Brabudu/ElectroneddasV3/Electronic_Electroneddas/ElectroV3_2_1.kicad_sch

## KiCad design Electronic_Electroneddas/ElectroV3_2_1.kicad_sch (2024-02-18)

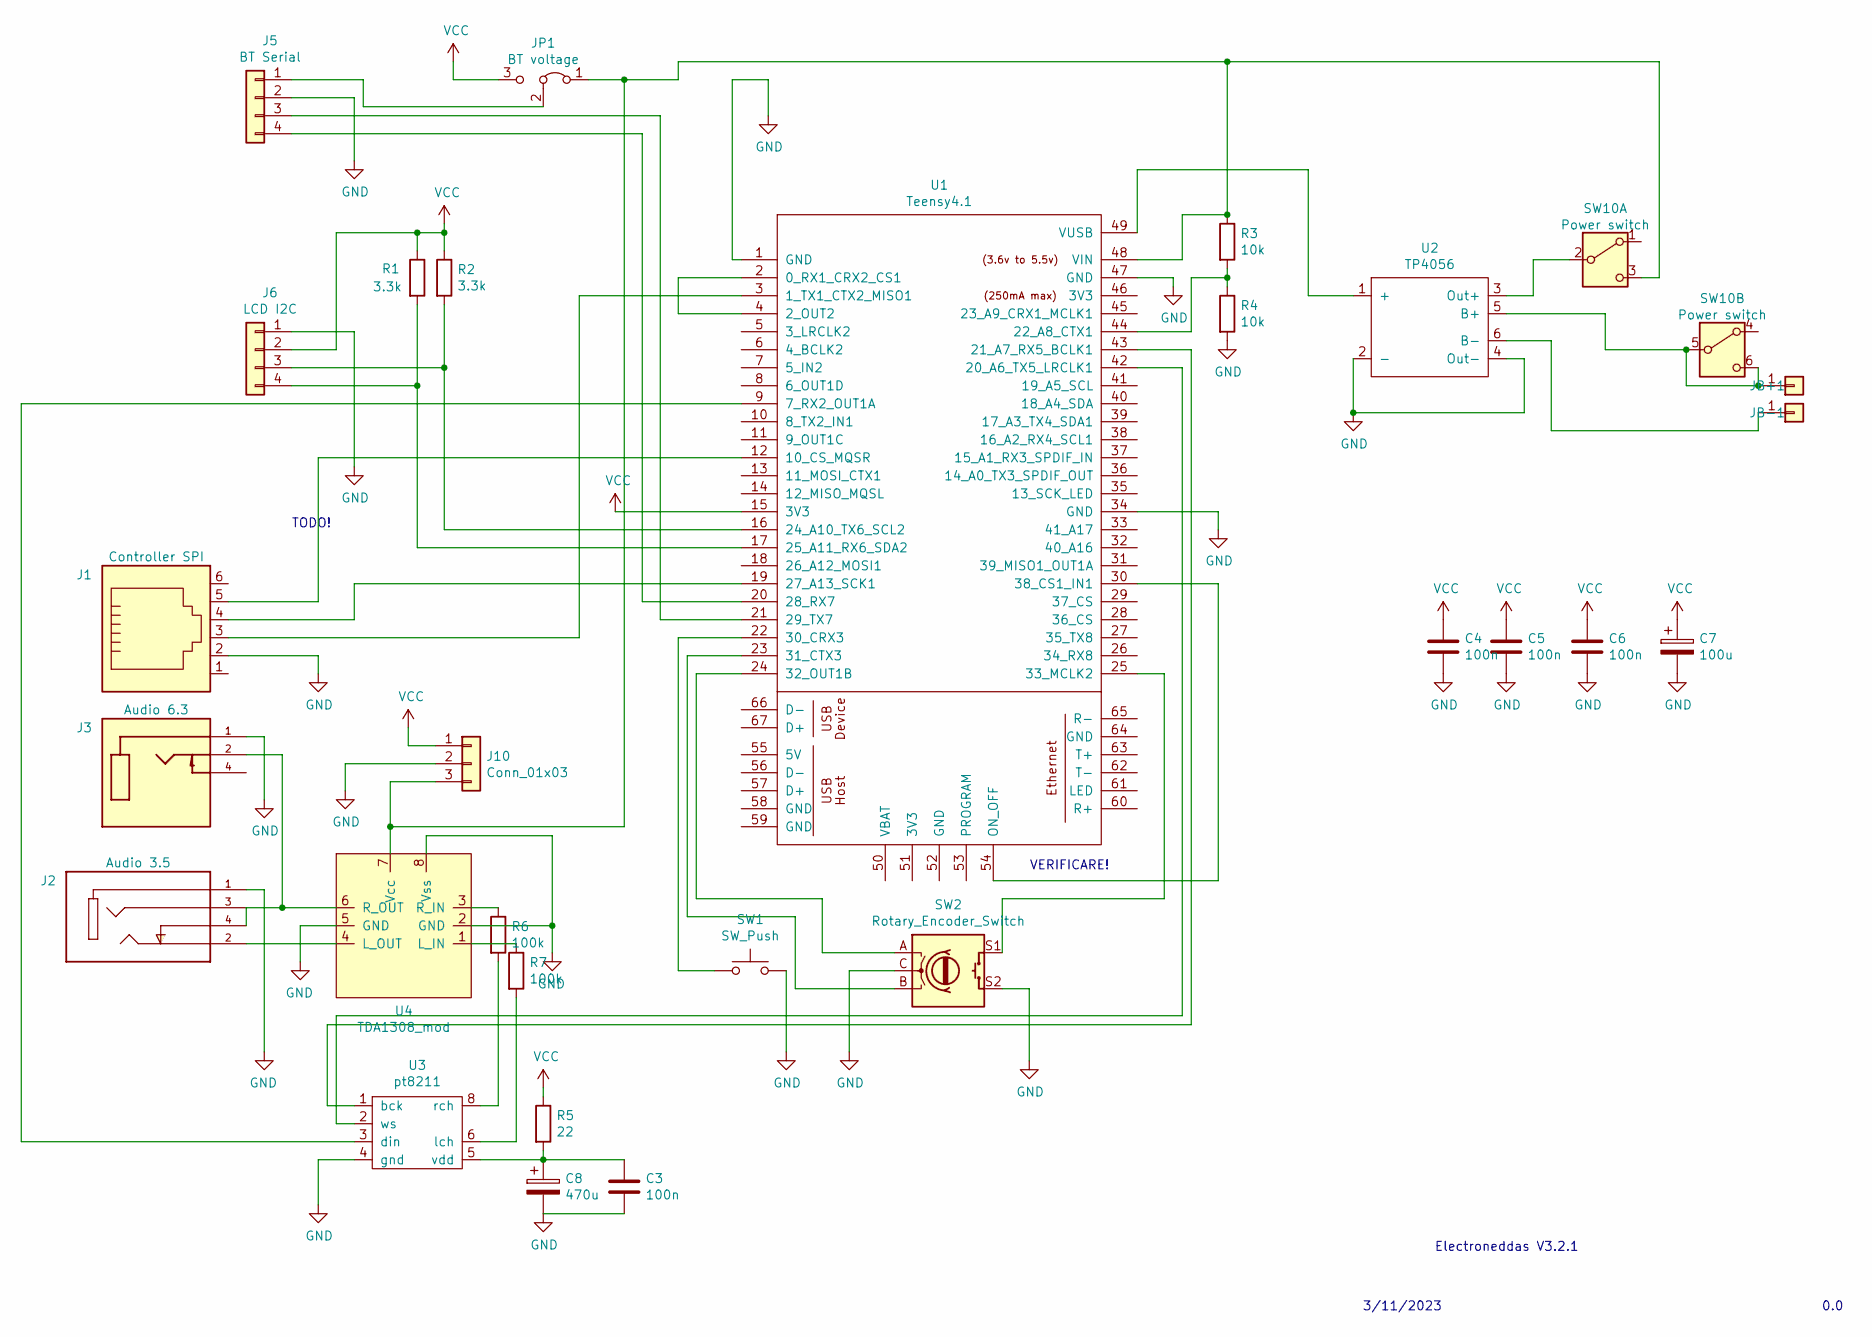
[picture p26: schematic ElectroV3_2_1.kicad_sch]

Parts:
C3, C4, C5, C6: 100n; C_Disc_D6.0mm_W2.5mm_P5.00mm
C7: 100u; CP_Radial_D8.0mm_P3.50mm
C8: 470u; CP_Radial_D8.0mm_P3.50mm
J1: Controller SPI; RJ12_Amphenol_54601
J2: Audio 3.5; CUI_SJ1-3534NG
J3: Audio 6.3; CUI_MJ-63022B; PARTREV 1.0
J5: BT Serial; PinHeader_1x04_P2.54mm_Vertical
J6: LCD I2C; PinHeader_1x04_P2.54mm_Vertical
J10: Conn_01x03; PinHeader_1x03_P2.54mm_Vertical
JB+1: Conn_01x01_Male; PinHeader_1x01_P2.54mm_Vertical
JB-1: Conn_01x01_Male; PinHeader_1x01_P2.54mm_Vertical
JP1: BT voltage; SolderJumper-3_P1.3mm_Bridged12_Pad1.0x1.5mm
R1, R2: 3.3k; R_Axial_DIN0207_L6.3mm_D2.5mm_P2.54mm_Vertical
R3, R4: 10k; R_Axial_DIN0207_L6.3mm_D2.5mm_P2.54mm_Vertical
R5: 22; R_Axial_DIN0207_L6.3mm_D2.5mm_P2.54mm_Vertical
R6, R7: 100k; R_Axial_DIN0207_L6.3mm_D2.5mm_P2.54mm_Vertical
SW1: SW_Push; SW_PUSH_6mm
SW2: Rotary_Encoder_Switch; RotaryEncoder_Alps_EC11E-Switch_Vertical_H20mm_CircularMoun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
SW10: Power switch; 6pin_vertical
U1: Teensy4.1; Teensy41
U2: TP4056
U3: pt8211; SOIC-8_3.9x4.9mm_P1.27mm
U4: TDA1308_mod; TDA1308

Connections:
GND: C3.2, C4.2, C5.2, C6.2, C7.2, C8.2, J1.2, J2.1, J3.1, J5.2, J6.1, J10.2, R4.2, SW1.2, SW2.C, SW2.S2, U1.1 (GND), U1.34 (GND), U1.47 (GND), U2.2 (-), U2.4 (Out-), U3.4 (gnd), U4.2 (GND), U4.5 (GND), U4.8 (Vss)
unnamed: C3.1, C8.1, R5.2, U3.5 (vdd)
unnamed: J1.3, U1.3 (1_TX1_CTX2_MISO1)
unnamed: J1.4, U1.19 (27_A13_SCK1)
unnamed: J1.5, U1.12 (10_CS_MQSR)
unnamed: J2.2, U4.4 (L_OUT)
unnamed: J2.3, J2.4, J3.2, U4.6 (R_OUT)
unnamed: J5.1, JP1.2 (C)
unnamed: J5.3, U1.21 (29_TX7)
unnamed: J5.4, U1.20 (28_RX7)
unnamed: J6.3, R2.2, U1.16 (24_A10_TX6_SCL2)
unnamed: J6.4, R1.2, U1.17 (25_A11_RX6_SDA2)
unnamed: J10.3, JP1.1 (A), R3.1, SW10.3 (C), U1.48 (VIN), U4.7 (Vcc)
unnamed: JB+1.1, SW10.5 (B), SW10.6 (C), U2.5 (B+)
unnamed: JB-1.1, U2.6 (B-)
unnamed: R3.2, R4.1, U1.44 (22_A8_CTX1)
unnamed: R6.1, U4.3 (R_IN)
unnamed: R6.2, U3.8 (rch)
unnamed: R7.1, U4.1 (L_IN)
unnamed: R7.2, U3.6 (lch)
unnamed: SW1.1, U1.22 (30_CRX3)
unnamed: SW2.A, U1.24 (32_OUT1B)
unnamed: SW2.B, U1.23 (31_CTX3)
unnamed: SW2.S1, U1.25 (33_MCLK2)
unnamed: SW10.2 (B), U2.3 (Out+)
unnamed: U1.2 (0_RX1_CRX2_CS1), U1.4 (2_OUT2)
unnamed: U1.9 (7_RX2_OUT1A), U3.3 (din)
unnamed: U1.30 (38_CS1_IN1), U1.54 (ON_OFF)
unnamed: U1.42 (20_A6_TX5_LRCLK1), U3.2 (ws)
unnamed: U1.43 (21_A7_RX5_BCLK1), U3.1 (bck)
unnamed: U1.49 (VUSB), U2.1 (+)
VCC: C4.1, C5.1, C6.1, C7.1, J6.2, J10.1, JP1.3 (B), R1.1, R2.1, R5.1, U1.15 (3V3)

Notes on the sheet:
TODO!
3/11/2023
VERIFICARE!
0.0
Electroneddas V3.2.1
