Brabudu/ElectroneddasV3/Teensy_Electroneddas/bitmap.h

const uint8_t sd_bitmap_16x11[] PROGMEM = {

  0xfe, 0x02, 0x02, 0x82, 0x82, 0x02, 0x82, 0x82, 0x4, 0x08, 0xf0,
  0x3f, 0x20, 0x29, 0x2a, 0x24, 0x20, 0x2f, 0x28, 0x27, 0x20, 0x3f

};

const uint8_t el_bitmap_48x48[] PROGMEM = {

  0xff, 0xff, 0xff, 0xff, 0xff, 0x7f, 0x3f, 0x1f, 0x1f, 0x0f, 0x07, 0x87, 0x83, 0x03, 0x03, 0x01, 0x01, 0x01, 0x01, 0x01, 0x01, 0x01, 0x81, 0xc1, 0xe1, 0x71, 0x39, 0x39, 0x71, 0xe1, 0xc1, 0x81, 0x01, 0x03, 0x03, 0x03, 0x07, 0x07, 0x0f, 0x1f, 0x1f, 0x3f, 0x7f, 0xff, 0xff, 0xff, 0xff, 0xff,

  0xff, 0x7f, 0x0f, 0x03, 0x01, 0x00, 0x00, 0x00, 0x00, 0x00, 0x00, 0xff, 0xff, 0x07, 0x0e, 0x1c, 0x38, 0x70, 0x38, 0x1c, 0x0e, 0x07, 0x03, 0x01, 0x00, 0x00, 0x00, 0x00, 0x00, 0x00, 0x01, 0x03, 0x07, 0x0e, 0x1c, 0x38, 0x70, 0xe0, 0xc0, 0x00, 0x00, 0x00, 0x00, 0x01, 0x03, 0x0f, 0x7f, 0xff,

  0xff, 0x00, 0x00, 0x00, 0x00, 0x00, 0x00, 0x00, 0x00, 0x00, 0x00, 0xff, 0xff, 0x00, 0x00, 0x00, 0x00, 0xc0, 0x30, 0x08, 0xc4, 0x24, 0x12, 0x92, 0x49, 0x49, 0x89, 0x12, 0x22, 0x44, 0x88, 0x10, 0x60, 0x80, 0x00, 0x00, 0x00, 0xff, 0xff, 0x00,
  0x00, 0x00, 0x00, 0x00, 0x00, 0x00, 0x00, 0xff,

  0xff, 0x00, 0x00, 0x00, 0x00, 0x00, 0x00, 0x00, 0x00, 0x00, 0x00, 0xff, 0xff, 0x00, 0x00, 0x00, 0x00, 0x07, 0x18, 0x20, 0x43, 0x44, 0x88, 0x93, 0x92, 0x90, 0x48, 0x47, 0x20, 0x18, 0x07, 0x00, 0x00, 0x07, 0x00, 0x00, 0x00, 0xff, 0xff, 0x00, 0x00, 0x00, 0x00, 0x00, 0x00, 0x00, 0x00, 0xff,

  0xff, 0xfe, 0xf0, 0xc0, 0x80, 0x00, 0x00, 0x00, 0x00, 0x00, 0x00, 0x07, 0x0f, 0x1c, 0x38, 0x70, 0xe0, 0xc0, 0x80, 0x00, 0x00, 0x00, 0x00, 0x00, 0x00, 0x80, 0xc0, 0xe0, 0x70, 0x38, 0x1c, 0x0e, 0x1c, 0x38, 0x70, 0xe0, 0xc0, 0xff, 0xff, 0x00, 0x00, 0x00, 0x00, 0x80, 0xc0, 0xf0, 0xfe, 0xff,

  0xff, 0xff, 0xff, 0xff, 0xff, 0xfe, 0xfc, 0xf8, 0xf8, 0xf0, 0xe0, 0xe0, 0xc0, 0xc0, 0xc0, 0x80, 0x80, 0x81, 0x83, 0x87, 0x8e, 0x9c, 0x9c, 0x8e, 0x87, 0x83, 0x81, 0x80, 0x80, 0x80, 0x80, 0x80, 0x80, 0xc0, 0xc0, 0xc0, 0xe1, 0xe3, 0xf3, 0xf8, 0xf8, 0xfc, 0xfe, 0xff, 0xff, 0xff, 0xff, 0xff
};

const uint8_t allpass_8x4[] PROGMEM = { 2, 2, 2, 2, 2, 2, 2, 2 };
const uint8_t lopass_8x4[] PROGMEM = { 1, 1, 1, 1, 1, 2, 4, 8 };
const uint8_t hipass_8x4[] PROGMEM = { 4, 4, 4, 4, 2, 1, 1, 1 };
