Brabudu/ElectroneddasV3/Teensy_Electroneddas/samples.h

const int16_t wtumbu[256] PROGMEM = {
  7923, -5048, -5108, 15113, 24533, 25788, 19247, 19861, 32763, 31736,
  22843, 20145, 19035, 10543, 4581, 15920, 16743, 1057, -1323, 4570, 2506, -4051, -4963, 550, 3522, 1978,
  -674, 114, 3609, 3050, 1812, 5513, 7429, 6219, 9187, 11880, 9607, 6870, 7682, 10941, 11283, 8811,
  7490, 8542, 11971, 12125, 7676, 3282, 2512, 5026, 4109, -60, -738, 1650, 2200, -1330, -3760, -2736,
  -1414, -667, 1865, 5145, 3596, 1103, 4191, 8407, 8162, 3802, 2623, 5574, 6998, 6824, 4750, 3674,
  5458, 5302, 4294, 3881, 2398, 899, 1678, 3882, 3339, 834, -656, -591, 1499, 3485, 2975, 1623,
  1716, 2685, 1975, 1110, 700, 1501, 4363, 5069, 2670, 1641, 2938, 4515, 6320, 8554, 8502, 6882,
  7785, 8749, 8102, 8085, 9528, 12218, 12916, 11443, 11250, 11348, 12190, 13803, 14074, 15207, 16695, 15049,
  11948, 10536, 10258, 8702, 6356, 6342, 7846, 6570, 4305, 6126, 9408, 8853, 5179, 2567, 4119, 6318,
  3466, -316, -793, -1143, -1734, -881, 701, 1141, 331, 2799, 6064, 4603, 2496, 1813, 527, -2932,
  -5416, -2436, 542, -317, -1747, -431, 2441, 1296, -771, 1035, 2982, 4568, 6031, 6908, 6717, 4783,
  4897, 6427, 5984, 5175, 5972, 7616, 7130, 5031, 3873, 2214, 1765, 1807, 860, 1930, 3441, 3379,
  3635, 3363, 3576, 4318, 3766, 3267, 4339, 7828, 9413, 5617, 3474, 4266, 4849, 6065, 5433, 4242,
  5522, 5181, 2734, 3036, 4502, 3404, 2701, 3574, 2491, 2522, 3631, 2669, 3145, 3183, 927, 1277,
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
  -11040, -10624, -10341, -10325, -10621, -11077, -11517, -11725, -11695, -11480, -11272, -11162, -11142, -11024, -10588, -9659,
  -8200, -6385, -4447, -2692, -1322, -440
};

const int16_t* waves[6] = { wtumbu, wtumbu2, wtumbu3, cab_md_po_sol, cab_md_c_mi, cab_ms_po_sol };
